callistix/phaduino/datasheets/Mini Push Button 1.png

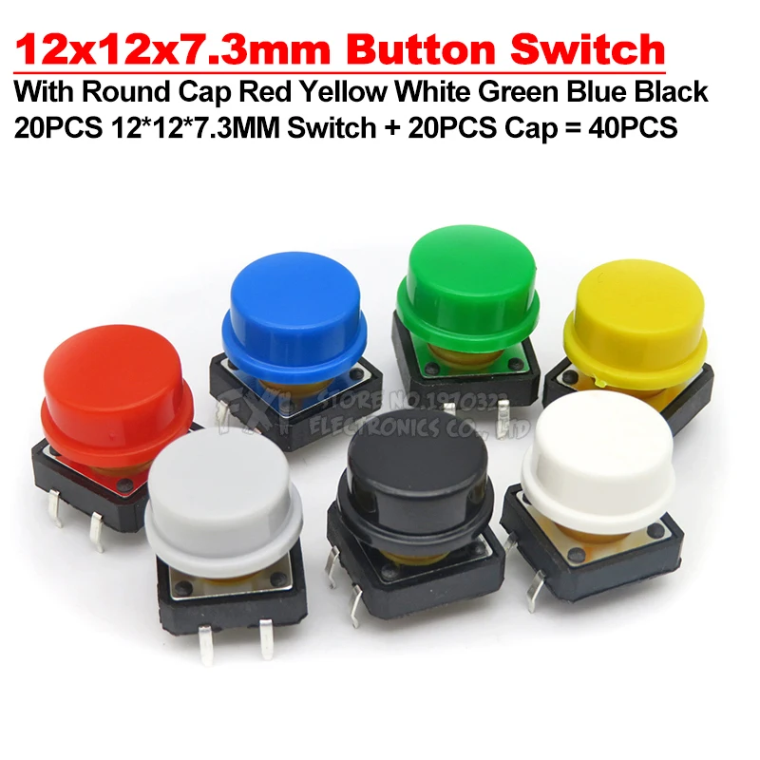
datasheets/Mini Push Button 1.png
