callistix/phaduino/datasheets/SR16 16mm Rotary Band Switch 1 Pole 5 Positions 2.png

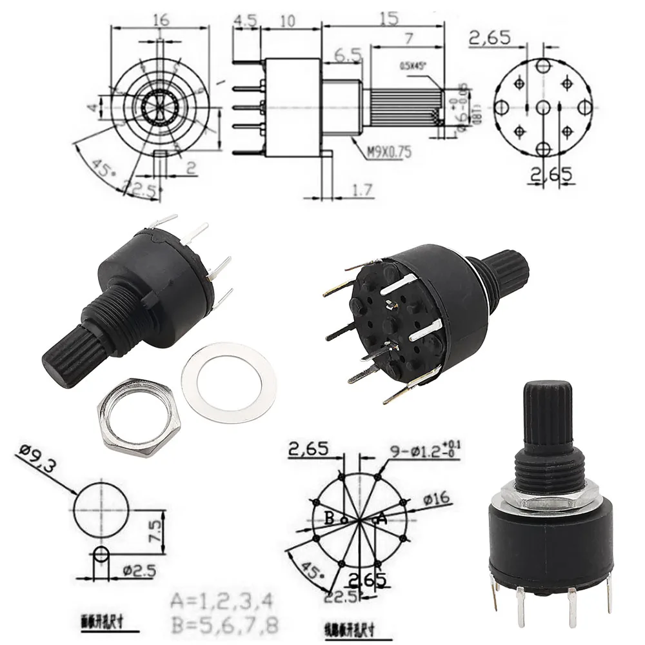
datasheets/SR16 16mm Rotary Band Switch 1 Pole 5 Positions 2.png
