callistix/phaduino/kicad/phaduino/phaduino.kicad_sch

## KiCad design kicad/phaduino/phaduino.kicad_sch (2024-05-12)

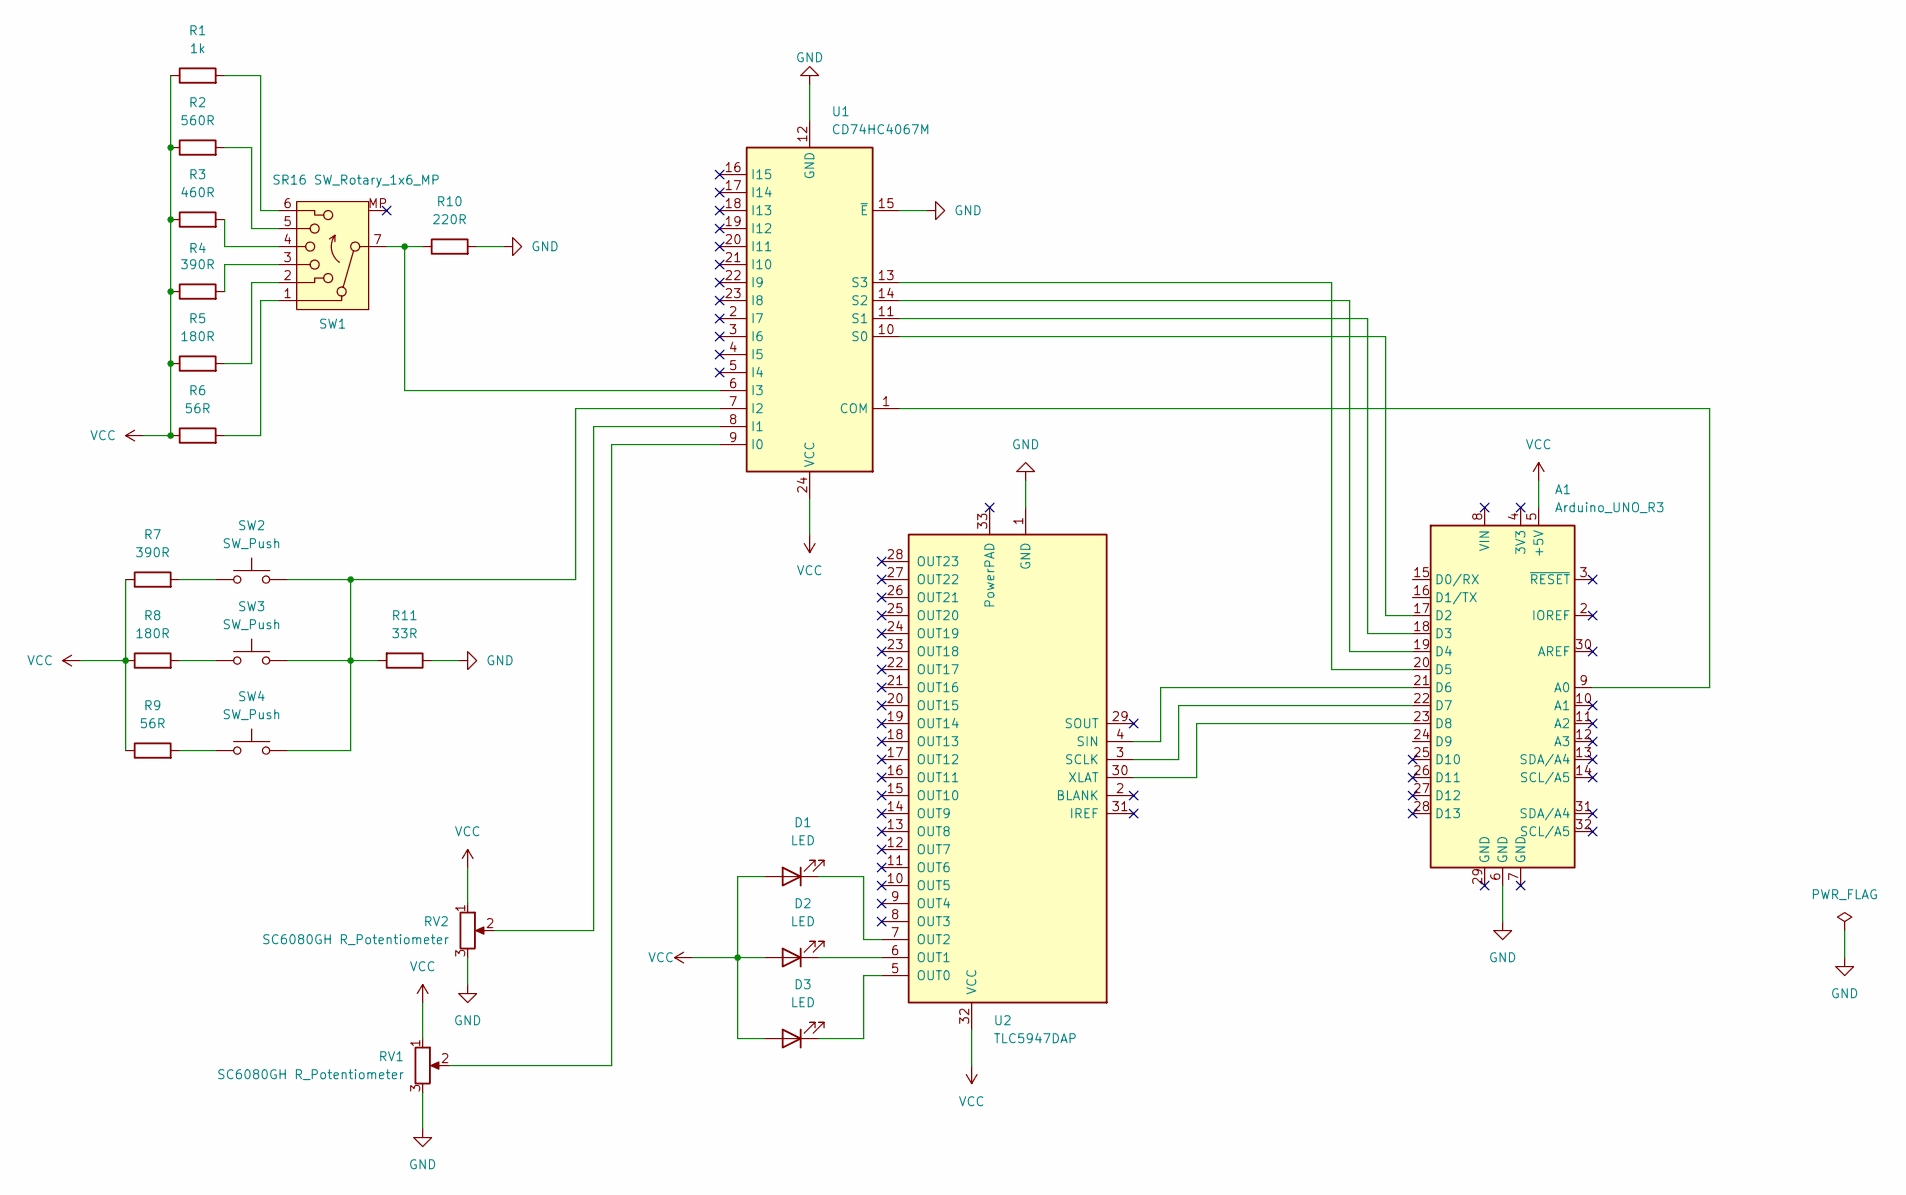
[picture p17: schematic phaduino.kicad_sch]

Parts:
A1: Arduino_UNO_R3
D1, D2, D3: LED
R1: 1k
R2: 560R
R3: 460R
R4, R7: 390R
R5, R8: 180R
R6, R9: 56R
R10: 220R
R11: 33R
RV1, RV2: SC6080GH R_Potentiometer
SW1: SR16 SW_Rotary_1x6_MP
SW2, SW3, SW4: SW_Push
U1: CD74HC4067M; SOIC-24W_7.5x15.4mm_P1.27mm
U2: TLC5947DAP; HTSSOP-32-1EP_6.1x11mm_P0.65mm_EP5.2x11mm_Mask4.11x4.36mm_T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

Connections:
GND: A1.6 (GND), R10.2, R11.1, RV1.3, RV2.3, U1.12 (GND), U1.15 (~E), U2.1 (GND)
unnamed: A1.9 (A0), U1.1 (COM)
unnamed: A1.17 (D2), U1.10 (S0)
unnamed: A1.18 (D3), U1.11 (S1)
unnamed: A1.19 (D4), U1.14 (S2)
unnamed: A1.20 (D5), U1.13 (S3)
unnamed: A1.21 (D6), U2.4 (SIN)
unnamed: A1.22 (D7), U2.3 (SCLK)
unnamed: A1.23 (D8), U2.30 (XLAT)
unnamed: D1.1 (K), U2.7 (OUT2)
unnamed: D2.1 (K), U2.6 (OUT1)
unnamed: D3.1 (K), U2.5 (OUT0)
unnamed: R1.2, SW1.6
unnamed: R2.2, SW1.5
unnamed: R3.2, SW1.4
unnamed: R4.2, SW1.3
unnamed: R5.2, SW1.2
unnamed: R6.2, SW1.1
unnamed: R7.2, SW2.1
unnamed: R8.2, SW3.1
unnamed: R9.2, SW4.1
unnamed: R10.1, SW1.7, U1.6 (I3)
unnamed: R11.2, SW2.2, SW3.2, SW4.2, U1.7 (I2)
unnamed: RV1.2, U1.9 (I0)
unnamed: RV2.2, U1.8 (I1)
VCC: A1.5 (+5V), D1.2 (A), D2.2 (A), D3.2 (A), R1.1, R2.1, R3.1, R4.1, R5.1, R6.1, R7.1, R8.1, R9.1, RV1.1, RV2.1, U1.24 (VCC), U2.32 (VCC)
