callistix/phaduino/sketch/oo_test_cpp/oo_test_cpp.ino

class LED {
    public:
};

class Mux {
    public:
};

class TLC {
    public:
};

class Control {
    public:
};

class ControlPot : public Control {
    public:
};

class ControlButtonArray3 : public Control {
    public:
};

class ControlSwitch5 : public Control {
    public:
};

class Section {
    public:
        std::vector<Control> control;
};


void setup(void) {

}


void loop(void) {

}
